mkahres/diagnosegeraetAudi20vTurbo/diagnoseGeraet/MusicManager.h

#ifndef MusicManager_h
#define MusicManager_h

#include "Constants.h"


class MusicManager
{
  public:
    MusicManager();
    void playStarWars();
    void playIt(int *melody, int notes, int wholenote);
};

#endif
